thecleverbanana/BECOv2/simulation/Webots/worlds/.apartment.jpg

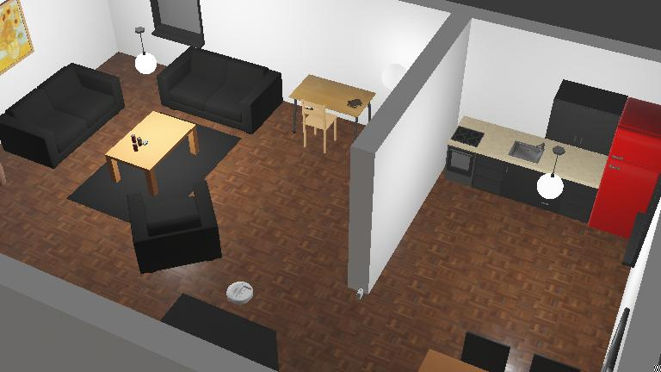
simulation/Webots/worlds/.apartment.jpg
