thecleverbanana/BECOv2/simulation/Webots/worlds/.crazyflie.jpg

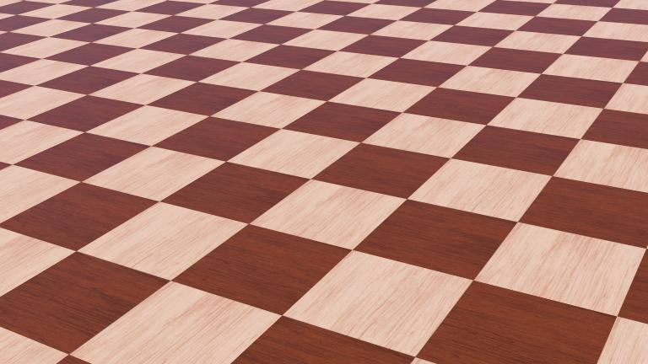
simulation/Webots/worlds/.crazyflie.jpg
