thecleverbanana/BECOv2/simulation/Webots/worlds/.moon.jpg

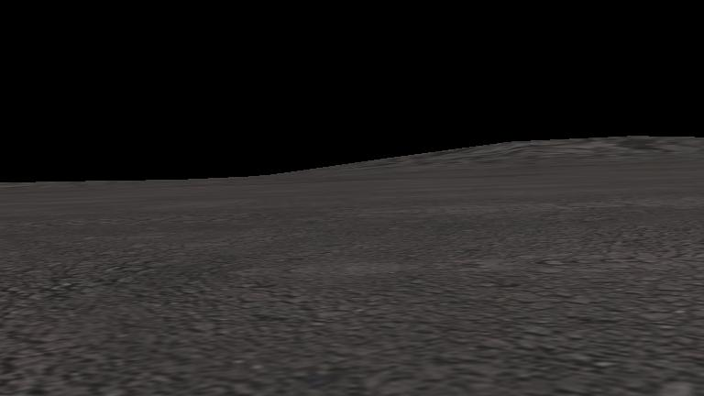
simulation/Webots/worlds/.moon.jpg
