thecleverbanana/BECOv2/CAD/l12_100mm_out.step

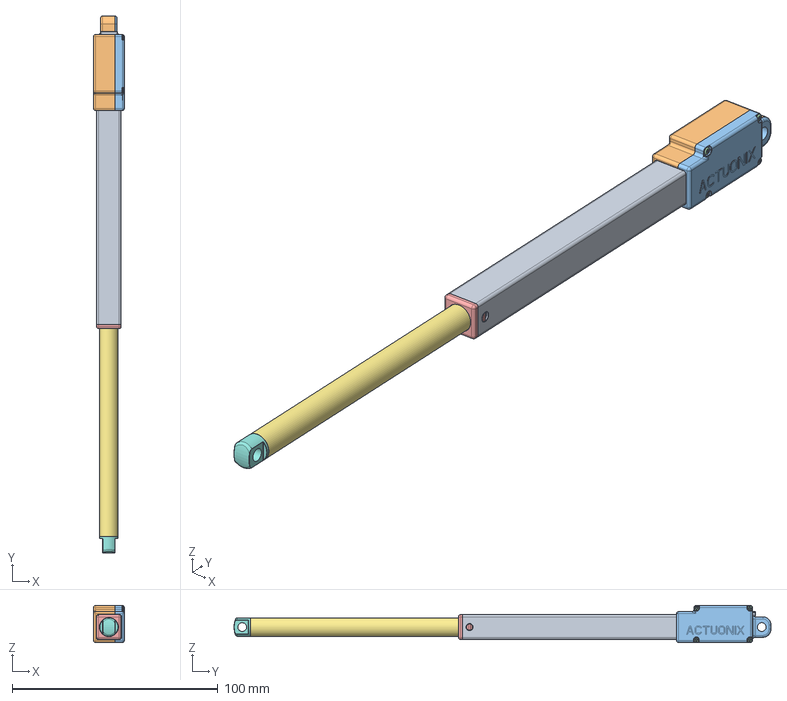
[picture p33: CAD file, 2025-06-12]
CAD/l12_100mm_out.step
15.1 x 261.0 x 18.0 mm
EXTENSION_10405_100MM
CLAMSHELL_BOT_10417
CLAMSHELL_TOP_10416
FASTENER_10427 x 4
GUIDE_10429
NUT_10419
SHAFT_10410_100MM
PLUG_10428
GROMMET_3_HOLE
