thecleverbanana/BECOv2/CAD/Base Plate Type 1.step

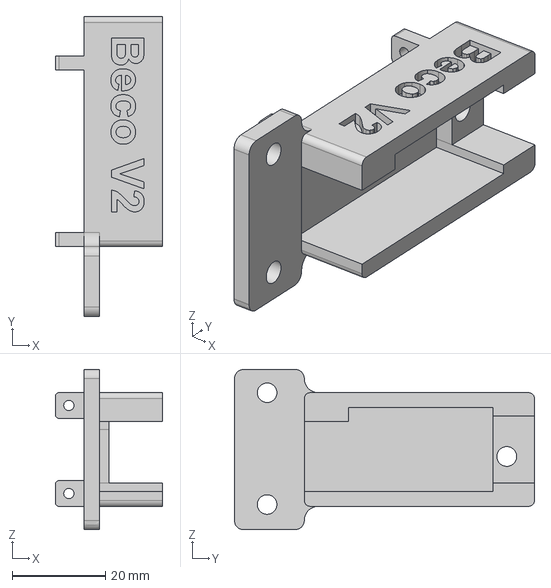
[picture p34: CAD file, 2025-06-12]
CAD/Base Plate Type 1.step
23.0 x 64.4 x 34.4 mm
