thecleverbanana/BECOv2/simulation/Gazebo/BECOV2_description/meshes/stl/SHAFT.stl

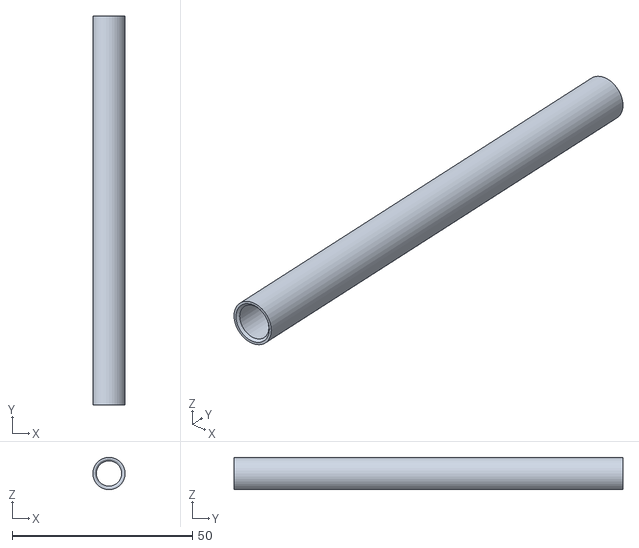
[picture p36: CAD file, 2025-05-25]
simulation/Gazebo/BECOV2_description/meshes/stl/SHAFT.stl
8.95 x 108.0 x 8.95
