thecleverbanana/BECOv2/mega2560/include/actuator.h

#ifndef ACTUATOR_H
#define ACTUATOR_H

#include <Arduino.h>

class Actuator {
public:
    Actuator(int pwmPin, int feedbackPin,
             float kp = 0.3, float kd = 0.01,
             int pwmMax = 255
        );

    float kp, kd;

    void setPosition(float pos);
    void setPosition(float pos, bool closedLoop);

    float getVoltage();
    float getPosition();

    void setvMin();              
    void setvMax();
    float getvMin();              
    float getvMax();

private:
    int pwmPin, feedbackPin;
    int pwmMax, rawMax, posMax;
    float frequency;      // Hz
    float omega;          // 2πf

    const float vRef = 3.3;
    const int   adcMax = 1023;
    float vMax = 2.2;
    float vMin = 0.0;
};

#endif
